hamzahaddaoui/AC-Adapter-with-Voltmeter/src/pic18f2420.h

#ifndef _PIC18F2420_H_
#define _PIC18F2420_H_

/*
 * C Header file for the Microchip PIC Microcontroller
 * PIC18F2420
 */
#ifndef _HTC_H_
#warning Header file pic18f2420.h included directly. Use #include <htc.h> instead.
#endif

/*
 * Register Definitions
 */

// Register: PORTA
extern volatile unsigned char           PORTA               @ 0xF80;
#ifndef _LIB_BUILD
asm("PORTA equ 0F80h");
#endif
// bitfield definitions
extern volatile union {
    struct {
        unsigned RA0                    :1;
        unsigned RA1                    :1;
        unsigned RA2                    :1;
        unsigned RA3                    :1;
        unsigned RA4                    :1;
        unsigned RA5                    :1;
        unsigned RA6                    :1;
        unsigned RA7                    :1;
    };
    struct {
        unsigned RA                     :8;
    };
    struct {
        unsigned AN0                    :1;
        unsigned AN1                    :1;
        unsigned AN2                    :1;
        unsigned AN3                    :1;
        unsigned T0CKI                  :1;
        unsigned AN4                    :1;
        unsigned OSC2                   :1;
        unsigned OSC1                   :1;
    };
    struct {
        unsigned                        :2;
        unsigned VREFN                  :1;
        unsigned VREFP                  :1;
        unsigned                        :1;
        unsigned SS                     :1;
        unsigned CLKO                   :1;
        unsigned CLKI                   :1;
    };
    struct {
        unsigned                        :5;
        unsigned NOT_SS                 :1;
    };
    struct {
        unsigned                        :2;
        unsigned CVREF                  :1;
        unsigned                        :2;
        unsigned nSS                    :1;
    };
    struct {
        unsigned                        :5;
        unsigned LVDIN                  :1;
    };
    struct {
        unsigned                        :5;
        unsigned HLVDIN                 :1;
    };
    struct {
        unsigned                        :4;
        unsigned C1OUT                  :1;
        unsigned C2OUT                  :1;
    };
    struct {
        unsigned                        :7;
        unsigned RJPU                   :1;
    };
    struct {
        unsigned ULPWUIN                :1;
    };
} PORTAbits @ 0xF80;

// Register: PORTB
extern volatile unsigned char           PORTB               @ 0xF81;
#ifndef _LIB_BUILD
asm("PORTB equ 0F81h");
#endif
// bitfield definitions
extern volatile union {
    struct {
        unsigned RB0                    :1;
        unsigned RB1                    :1;
        unsigned RB2                    :1;
        unsigned RB3                    :1;
        unsigned RB4                    :1;
        unsigned RB5                    :1;
        unsigned RB6                    :1;
        unsigned RB7                    :1;
    };
    struct {
        unsigned RB                     :8;
    };
    struct {
        unsigned INT0                   :1;
        unsigned INT1                   :1;
        unsigned INT2                   :1;
        unsigned CCP2                   :1;
        unsigned KBI0                   :1;
        unsigned KBI1                   :1;
        unsigned KBI2                   :1;
        unsigned KBI3                   :1;
    };
    struct {
        unsigned AN12                   :1;
        unsigned AN10                   :1;
        unsigned AN8                    :1;
        unsigned AN9                    :1;
        unsigned AN11                   :1;
        unsigned PGM                    :1;
        unsigned PGC                    :1;
        unsigned PGD                    :1;
    };
    struct {
        unsigned FLT0                   :1;
    };
    struct {
        unsigned                        :3;
        unsigned CCP2_PA2               :1;
    };
} PORTBbits @ 0xF81;

// Register: PORTC
extern volatile unsigned char           PORTC               @ 0xF82;
#ifndef _LIB_BUILD
asm("PORTC equ 0F82h");
#endif
// bitfield definitions
extern volatile union {
    struct {
        unsigned RC0                    :1;
        unsigned RC1                    :1;
        unsigned RC2                    :1;
        unsigned RC3                    :1;
        unsigned RC4                    :1;
        unsigned RC5                    :1;
        unsigned RC6                    :1;
        unsigned RC7                    :1;
    };
    struct {
        unsigned RC                     :8;
    };
    struct {
        unsigned T1OSO                  :1;
        unsigned T1OSI                  :1;
        unsigned CCP1                   :1;
        unsigned SCK                    :1;
        unsigned SDI                    :1;
        unsigned SDO                    :1;
        unsigned TX                     :1;
        unsigned RX                     :1;
    };
    struct {
        unsigned T13CKI                 :1;
        unsigned CCP2                   :1;
        unsigned                        :1;
        unsigned SCL                    :1;
        unsigned SDA                    :1;
        unsigned                        :1;
        unsigned CK                     :1;
        unsigned DT                     :1;
    };
    struct {
        unsigned T1CKI                  :1;
    };
    struct {
        unsigned                        :2;
        unsigned PA1                    :1;
    };
    struct {
        unsigned                        :1;
        unsigned PA2                    :1;
    };
} PORTCbits @ 0xF82;

// Register: PORTE
extern volatile unsigned char           PORTE               @ 0xF84;
#ifndef _LIB_BUILD
asm("PORTE equ 0F84h");
#endif
// bitfield definitions
extern volatile union {
    struct {
        unsigned                        :3;
        unsigned RE3                    :1;
    };
    struct {
        unsigned RE                     :8;
    };
    struct {
        unsigned                        :3;
        unsigned MCLR                   :1;
    };
    struct {
        unsigned                        :3;
        unsigned NOT_MCLR               :1;
    };
    struct {
        unsigned                        :3;
        unsigned nMCLR                  :1;
    };
    struct {
        unsigned                        :3;
        unsigned VPP                    :1;
    };
    struct {
        unsigned                        :2;
        unsigned CCP10                  :1;
    };
    struct {
        unsigned                        :7;
        unsigned CCP2E                  :1;
    };
    struct {
        unsigned                        :6;
        unsigned CCP6E                  :1;
    };
    struct {
        unsigned                        :5;
        unsigned CCP7E                  :1;
    };
    struct {
        unsigned                        :4;
        unsigned CCP8E                  :1;
    };
    struct {
        unsigned                        :3;
        unsigned CCP9E                  :1;
    };
    struct {
        unsigned                        :2;
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
        unsigned RB2                    :1;
        unsigned RB3                    :1;
        unsigned RB4                    :1;
        unsigned RB5                    :1;
        unsigned RB6                    :1;
        unsigned RB7                    :1;
    };
} DDRBbits @ 0xF93;

// Register: TRISC
extern volatile unsigned char           TRISC               @ 0xF94;
#ifndef _LIB_BUILD
asm("TRISC equ 0F94h");
#endif
// aliases
extern volatile unsigned char           DDRC                @ 0xF94;
#ifndef _LIB_BUILD
asm("DDRC equ 0F94h");
#endif
// bitfield definitions
extern volatile union {
    struct {
        unsigned TRISC0                 :1;
        unsigned TRISC1                 :1;
        unsigned TRISC2                 :1;
        unsigned TRISC3                 :1;
        unsigned TRISC4                 :1;
        unsigned TRISC5                 :1;
        unsigned TRISC6                 :1;
        unsigned TRISC7                 :1;
    };
    struct {
        unsigned TRISC                  :8;
    };
    struct {
        unsigned RC0                    :1;
        unsigned RC1                    :1;
        unsigned RC2                    :1;
        unsigned RC3                    :1;
        unsigned RC4                    :1;
        unsigned RC5                    :1;
        unsigned RC6                    :1;
        unsigned RC7                    :1;
    };
} TRISCbits @ 0xF94;
// alias bitfield definitions
extern volatile union {
    struct {
        unsigned TRISC0                 :1;
        unsigned TRISC1                 :1;
        unsigned TRISC2                 :1;
        unsigned TRISC3                 :1;
        unsigned TRISC4                 :1;
        unsigned TRISC5                 :1;
        unsigned TRISC6                 :1;
        unsigned TRISC7                 :1;
    };
    struct {
        unsigned TRISC                  :8;
    };
    struct {
        unsigned RC0                    :1;
        unsigned RC1                    :1;
        unsigned RC2                    :1;
        unsigned RC3                    :1;
        unsigned RC4                    :1;
        unsigned RC5                    :1;
        unsigned RC6                    :1;
        unsigned RC7                    :1;
    };
} DDRCbits @ 0xF94;

// Register: OSCTUNE
extern volatile unsigned char           OSCTUNE             @ 0xF9B;
#ifndef _LIB_BUILD
asm("OSCTUNE equ 0F9Bh");
#endif
// bitfield definitions
extern volatile union {
    struct {
        unsigned TUN                    :5;
        unsigned                        :1;
        unsigned PLLEN                  :1;
        unsigned INTSRC                 :1;
    };
    struct {
        unsigned TUN0                   :1;
        unsigned TUN1                   :1;
        unsigned TUN2                   :1;
        unsigned TUN3                   :1;
        unsigned TUN4                   :1;
    };
} OSCTUNEbits @ 0xF9B;

// Register: PIE1
extern volatile unsigned char           PIE1                @ 0xF9D;
#ifndef _LIB_BUILD
asm("PIE1 equ 0F9Dh");
#endif
// bitfield definitions
extern volatile union {
    struct {
        unsigned TMR1IE                 :1;
        unsigned TMR2IE                 :1;
        unsigned CCP1IE                 :1;
        unsigned SSPIE                  :1;
        unsigned TXIE                   :1;
        unsigned RCIE                   :1;
        unsigned ADIE                   :1;
    };
    struct {
        unsigned                        :5;
        unsigned RC1IE                  :1;
    };
    struct {
        unsigned                        :4;
        unsigned TX1IE                  :1;
    };
} PIE1bits @ 0xF9D;

// Register: PIR1
extern volatile unsigned char           PIR1                @ 0xF9E;
#ifndef _LIB_BUILD
asm("PIR1 equ 0F9Eh");
#endif
// bitfield definitions
extern volatile union {
    struct {
        unsigned TMR1IF                 :1;
        unsigned TMR2IF                 :1;
        unsigned CCP1IF                 :1;
        unsigned SSPIF                  :1;
        unsigned TXIF                   :1;
        unsigned RCIF                   :1;
        unsigned ADIF                   :1;
    };
    struct {
        unsigned TMR1IF                 :1;
        unsigned TMR2IF                 :1;
        unsigned CCP1IF                 :1;
        unsigned SSPIF                  :1;
        unsigned                        :2;
        unsigned ADIF                   :1;
    };
    struct {
        unsigned                        :5;
        unsigned RC1IF                  :1;
    };
    struct {
        unsigned                        :4;
        unsigned TX1IF                  :1;
    };
} PIR1bits @ 0xF9E;

// Register: IPR1
extern volatile unsigned char           IPR1                @ 0xF9F;
#ifndef _LIB_BUILD
asm("IPR1 equ 0F9Fh");
#endif
// bitfield definitions
extern volatile union {
    struct {
        unsigned TMR1IP                 :1;
        unsigned TMR2IP                 :1;
        unsigned CCP1IP                 :1;
        unsigned SSPIP                  :1;
        unsigned TXIP                   :1;
        unsigned RCIP                   :1;
        unsigned ADIP                   :1;
    };
    struct {
        unsigned                        :5;
        unsigned RC1IP                  :1;
    };
    struct {
        unsigned                        :4;
        unsigned TX1IP                  :1;
    };
} IPR1bits @ 0xF9F;

// Register: PIE2
extern volatile unsigned char           PIE2                @ 0xFA0;
#ifndef _LIB_BUILD
asm("PIE2 equ 0FA0h");
#endif
// bitfield definitions
extern volatile union {
    struct {
        unsigned CCP2IE                 :1;
        unsigned TMR3IE                 :1;
        unsigned HLVDIE                 :1;
        unsigned BCLIE                  :1;
        unsigned EEIE                   :1;
        unsigned                        :1;
        unsigned CMIE                   :1;
        unsigned OSCFIE                 :1;
    };
    struct {
        unsigned                        :2;
        unsigned LVDIE                  :1;
    };
} PIE2bits @ 0xFA0;

// Register: PIR2
extern volatile unsigned char           PIR2                @ 0xFA1;
#ifndef _LIB_BUILD
asm("PIR2 equ 0FA1h");
#endif
// bitfield definitions
extern volatile union {
    struct {
        unsigned CCP2IF                 :1;
        unsigned TMR3IF                 :1;
        unsigned HLVDIF                 :1;
        unsigned BCLIF                  :1;
        unsigned EEIF                   :1;
        unsigned                        :1;
        unsigned CMIF                   :1;
        unsigned OSCFIF                 :1;
    };
    struct {
        unsigned                        :2;
        unsigned LVDIF                  :1;
    };
} PIR2bits @ 0xFA1;

// Register: IPR2
extern volatile unsigned char           IPR2                @ 0xFA2;
#ifndef _LIB_BUILD
asm("IPR2 equ 0FA2h");
#endif
// bitfield definitions
extern volatile union {
    struct {
        unsigned CCP2IP                 :1;
        unsigned TMR3IP                 :1;
        unsigned HLVDIP                 :1;
        unsigned BCLIP                  :1;
        unsigned EEIP                   :1;
        unsigned                        :1;
        unsigned CMIP                   :1;
        unsigned OSCFIP                 :1;
    };
    struct {
        unsigned                        :2;
        unsigned LVDIP                  :1;
    };
} IPR2bits @ 0xFA2;

// Register: EECON1
extern volatile unsigned char           EECON1              @ 0xFA6;
#ifndef _LIB_BUILD
asm("EECON1 equ 0FA6h");
#endif
// bitfield definitions
extern volatile union {
    struct {
        unsigned RD                     :1;
        unsigned WR                     :1;
        unsigned WREN                   :1;
        unsigned WRERR                  :1;
        unsigned FREE                   :1;
        unsigned                        :1;
        unsigned CFGS                   :1;
        unsigned EEPGD                  :1;
    };
    struct {
        unsigned                        :6;
        unsigned EEFS                   :1;
    };
} EECON1bits @ 0xFA6;

// Register: EECON2
extern volatile unsigned char           EECON2              @ 0xFA7;
#ifndef _LIB_BUILD
asm("EECON2 equ 0FA7h");
#endif
// bitfield definitions
extern volatile union {
    struct {
        unsigned EECON2                 :8;
    };
} EECON2bits @ 0xFA7;

// Register: EEDATA
extern volatile unsigned char           EEDATA              @ 0xFA8;
#ifndef _LIB_BUILD
asm("EEDATA equ 0FA8h");
#endif
// bitfield definitions
extern volatile union {
    struct {
        unsigned EEDATA                 :8;
    };
} EEDATAbits @ 0xFA8;

// Register: EEADR
extern volatile unsigned char           EEADR               @ 0xFA9;
#ifndef _LIB_BUILD
asm("EEADR equ 0FA9h");
#endif
// bitfield definitions
extern volatile union {
    struct {
        unsigned EEADR                  :8;
    };
} EEADRbits @ 0xFA9;

// Register: RCSTA
extern volatile unsigned char           RCSTA               @ 0xFAB;
#ifndef _LIB_BUILD
asm("RCSTA equ 0FABh");
#endif
// aliases
extern volatile unsigned char           RCSTA1              @ 0xFAB;
#ifndef _LIB_BUILD
asm("RCSTA1 equ 0FABh");
#endif
// bitfield definitions
extern volatile union {
    struct {
        unsigned RX9D                   :1;
        unsigned OERR                   :1;
        unsigned FERR                   :1;
        unsigned ADDEN                  :1;
        unsigned CREN                   :1;
        unsigned SREN                   :1;
        unsigned RX9                    :1;
        unsigned SPEN                   :1;
    };
    struct {
        unsigned                        :3;
        unsigned ADEN                   :1;
    };
    struct {
        unsigned                        :5;
        unsigned SRENA                  :1;
    };
} RCSTAbits @ 0xFAB;
// alias bitfield definitions
extern volatile union {
    struct {
        unsigned RX9D                   :1;
        unsigned OERR                   :1;
        unsigned FERR                   :1;
        unsigned ADDEN                  :1;
        unsigned CREN                   :1;
        unsigned SREN                   :1;
        unsigned RX9                    :1;
        unsigned SPEN                   :1;
    };
    struct {
        unsigned                        :3;
        unsigned ADEN                   :1;
    };
    struct {
        unsigned                        :5;
        unsigned SRENA                  :1;
    };
} RCSTA1bits @ 0xFAB;

// Register: TXSTA
extern volatile unsigned char           TXSTA               @ 0xFAC;
#ifndef _LIB_BUILD
asm("TXSTA equ 0FACh");
#endif
// aliases
extern volatile unsigned char           TXSTA1              @ 0xFAC;
#ifndef _LIB_BUILD
asm("TXSTA1 equ 0FACh");
#endif
// bitfield definitions
extern volatile union {
    struct {
        unsigned TX9D                   :1;
        unsigned TRMT                   :1;
        unsigned BRGH                   :1;
        unsigned SENDB                  :1;
        unsigned SYNC                   :1;
        unsigned TXEN                   :1;
        unsigned TX9                    :1;
        unsigned CSRC                   :1;
    };
    struct {
        unsigned                        :2;
        unsigned BRGH1                  :1;
    };
    struct {
        unsigned                        :7;
        unsigned CSRC1                  :1;
    };
    struct {
        unsigned                        :3;
        unsigned SENDB1                 :1;
    };
    struct {
        unsigned                        :4;
        unsigned SYNC1                  :1;
    };
    struct {
        unsigned                        :1;
        unsigned TRMT1                  :1;
    };
    struct {
        unsigned                        :6;
        unsigned TX91                   :1;
    };
    struct {
        unsigned TX9D1                  :1;
    };
    struct {
        unsigned                        :5;
        unsigned TXEN1                  :1;
    };
} TXSTAbits @ 0xFAC;
// alias bitfield definitions
extern volatile union {
    struct {
        unsigned TX9D                   :1;
        unsigned TRMT                   :1;
        unsigned BRGH                   :1;
        unsigned SENDB                  :1;
        unsigned SYNC                   :1;
        unsigned TXEN                   :1;
        unsigned TX9                    :1;
        unsigned CSRC                   :1;
    };
    struct {
        unsigned                        :2;
        unsigned BRGH1                  :1;
    };
    struct {
        unsigned                        :7;
        unsigned CSRC1                  :1;
    };
    struct {
        unsigned                        :3;
        unsigned SENDB1                 :1;
    };
    struct {
        unsigned                        :4;
        unsigned SYNC1                  :1;
    };
    struct {
        unsigned                        :1;
        unsigned TRMT1                  :1;
    };
    struct {
        unsigned                        :6;
        unsigned TX91                   :1;
    };
    struct {
        unsigned TX9D1                  :1;
    };
    struct {
        unsigned                        :5;
        unsigned TXEN1                  :1;
    };
} TXSTA1bits @ 0xFAC;

// Register: TXREG
extern volatile unsigned char           TXREG               @ 0xFAD;
#ifndef _LIB_BUILD
asm("TXREG equ 0FADh");
#endif
// aliases
extern volatile unsigned char           TXREG1              @ 0xFAD;
#ifndef _LIB_BUILD
asm("TXREG1 equ 0FADh");
#endif
// bitfield definitions
extern volatile union {
    struct {
        unsigned TXREG                  :8;
    };
} TXREGbits @ 0xFAD;
// alias bitfield definitions
extern volatile union {
    struct {
        unsigned TXREG                  :8;
    };
} TXREG1bits @ 0xFAD;

// Register: RCREG
extern volatile unsigned char           RCREG               @ 0xFAE;
#ifndef _LIB_BUILD
asm("RCREG equ 0FAEh");
#endif
// aliases
extern volatile unsigned char           RCREG1              @ 0xFAE;
#ifndef _LIB_BUILD
asm("RCREG1 equ 0FAEh");
#endif
// bitfield definitions
extern volatile union {
    struct {
        unsigned RCREG                  :8;
    };
} RCREGbits @ 0xFAE;
// alias bitfield definitions
extern volatile union {
    struct {
        unsigned RCREG                  :8;
    };
} RCREG1bits @ 0xFAE;

// Register: SPBRG
extern volatile unsigned char           SPBRG               @ 0xFAF;
#ifndef _LIB_BUILD
asm("SPBRG equ 0FAFh");
#endif
// aliases
extern volatile unsigned char           SPBRG1              @ 0xFAF;
#ifndef _LIB_BUILD
asm("SPBRG1 equ 0FAFh");
#endif
// bitfield definitions
extern volatile union {
    struct {
        unsigned SPBRG                  :8;
    };
} SPBRGbits @ 0xFAF;
// alias bitfield definitions
extern volatile union {
    struct {
        unsigned SPBRG                  :8;
    };
} SPBRG1bits @ 0xFAF;

// Register: SPBRGH
extern volatile unsigned char           SPBRGH              @ 0xFB0;
#ifndef _LIB_BUILD
asm("SPBRGH equ 0FB0h");
#endif
// bitfield definitions
extern volatile union {
    struct {
        unsigned SPBRGH                 :8;
    };
} SPBRGHbits @ 0xFB0;

// Register: T3CON
extern volatile unsigned char           T3CON               @ 0xFB1;
#ifndef _LIB_BUILD
asm("T3CON equ 0FB1h");
#endif
// bitfield definitions
extern volatile union {
    struct {
        unsigned                        :2;
        unsigned NOT_T3SYNC             :1;
    };
    struct {
        unsigned TMR3ON                 :1;
        unsigned TMR3CS                 :1;
        unsigned nT3SYNC                :1;
        unsigned T3CCP1                 :1;
        unsigned T3CKPS                 :2;
        unsigned T3CCP2                 :1;
        unsigned RD16                   :1;
    };
    struct {
        unsigned                        :2;
        unsigned T3SYNC                 :1;
        unsigned                        :1;
        unsigned T3CKPS0                :1;
        unsigned T3CKPS1                :1;
    };
    struct {
        unsigned                        :7;
        unsigned RD163                  :1;
    };
    struct {
        unsigned                        :3;
        unsigned SOSCEN3                :1;
    };
    struct {
        unsigned                        :7;
        unsigned T3RD16                 :1;
    };
} T3CONbits @ 0xFB1;

// Register: TMR3
extern volatile unsigned short          TMR3                @ 0xFB2;
#ifndef _LIB_BUILD
asm("TMR3 equ 0FB2h");
#endif
// bitfield definitions
extern volatile union {
    struct {
        unsigned TMR3                   :16;
    };
} TMR3bits @ 0xFB2;

// Register: TMR3L
extern volatile unsigned char           TMR3L               @ 0xFB2;
#ifndef _LIB_BUILD
asm("TMR3L equ 0FB2h");
#endif
// bitfield definitions
extern volatile union {
    struct {
        unsigned TMR3L                  :8;
    };
} TMR3Lbits @ 0xFB2;

// Register: TMR3H
extern volatile unsigned char           TMR3H               @ 0xFB3;
#ifndef _LIB_BUILD
asm("TMR3H equ 0FB3h");
#endif
// bitfield definitions
extern volatile union {
    struct {
        unsigned TMR3H                  :8;
    };
} TMR3Hbits @ 0xFB3;

// Register: CMCON
extern volatile unsigned char           CMCON               @ 0xFB4;
#ifndef _LIB_BUILD
asm("CMCON equ 0FB4h");
#endif
// bitfield definitions
extern volatile union {
    struct {
        unsigned CM                     :3;
        unsigned CIS                    :1;
        unsigned C1INV                  :1;
        unsigned C2INV                  :1;
        unsigned C1OUT                  :1;
        unsigned C2OUT                  :1;
    };
    struct {
        unsigned CM0                    :1;
        unsigned CM1                    :1;
        unsigned CM2                    :1;
    };
    struct {
        unsigned CMEN0                  :1;
    };
    struct {
        unsigned                        :1;
        unsigned CMEN1                  :1;
    };
    struct {
        unsigned                        :2;
        unsigned CMEN2                  :1;
    };
} CMCONbits @ 0xFB4;

// Register: CVRCON
extern volatile unsigned char           CVRCON              @ 0xFB5;
#ifndef _LIB_BUILD
asm("CVRCON equ 0FB5h");
#endif
// bitfield definitions
extern volatile union {
    struct {
        unsigned CVR                    :4;
        unsigned CVRSS                  :1;
        unsigned CVRR                   :1;
        unsigned CVROE                  :1;
        unsigned CVREN                  :1;
    };
    struct {
        unsigned CVR0                   :1;
        unsigned CVR1                   :1;
        unsigned CVR2                   :1;
        unsigned CVR3                   :1;
    };
    struct {
        unsigned                        :6;
        unsigned CVROEN                 :1;
    };
} CVRCONbits @ 0xFB5;

// Register: ECCP1AS
extern volatile unsigned char           ECCP1AS             @ 0xFB6;
#ifndef _LIB_BUILD
asm("ECCP1AS equ 0FB6h");
#endif
// aliases
extern volatile unsigned char           ECCPAS              @ 0xFB6;
#ifndef _LIB_BUILD
asm("ECCPAS equ 0FB6h");
#endif
// bitfield definitions
extern volatile union {
    struct {
        unsigned                        :2;
        unsigned PSSAC                  :2;
        unsigned ECCPAS                 :3;
        unsigned ECCPASE                :1;
    };
    struct {
        unsigned                        :2;
        unsigned PSSAC0                 :1;
        unsigned PSSAC1                 :1;
        unsigned ECCPAS0                :1;
        unsigned ECCPAS1                :1;
        unsigned ECCPAS2                :1;
    };
} ECCP1ASbits @ 0xFB6;
// alias bitfield definitions
extern volatile union {
    struct {
        unsigned                        :2;
        unsigned PSSAC                  :2;
        unsigned ECCPAS                 :3;
        unsigned ECCPASE                :1;
    };
    struct {
        unsigned                        :2;
        unsigned PSSAC0                 :1;
        unsigned PSSAC1                 :1;
        unsigned ECCPAS0                :1;
        unsigned ECCPAS1                :1;
        unsigned ECCPAS2                :1;
    };
} ECCPASbits @ 0xFB6;

// Register: PWM1CON
extern volatile unsigned char           PWM1CON             @ 0xFB7;
#ifndef _LIB_BUILD
asm("PWM1CON equ 0FB7h");
#endif
// aliases
extern volatile unsigned char           ECCP1DEL            @ 0xFB7;
#ifndef _LIB_BUILD
asm("ECCP1DEL equ 0FB7h");
#endif
// bitfield definitions
extern volatile union {
    struct {
        unsigned                        :7;
        unsigned PRSEN                  :1;
    };
} PWM1CONbits @ 0xFB7;
// alias bitfield definitions
extern volatile union {
    struct {
        unsigned                        :7;
        unsigned PRSEN                  :1;
    };
} ECCP1DELbits @ 0xFB7;

// Register: BAUDCON
extern volatile unsigned char           BAUDCON             @ 0xFB8;
#ifndef _LIB_BUILD
asm("BAUDCON equ 0FB8h");
#endif
// aliases
extern volatile unsigned char           BAUDCTL             @ 0xFB8;
#ifndef _LIB_BUILD
asm("BAUDCTL equ 0FB8h");
#endif
// bitfield definitions
extern volatile union {
    struct {
        unsigned ABDEN                  :1;
        unsigned WUE                    :1;
        unsigned                        :1;
        unsigned BRG16                  :1;
        unsigned TXCKP                  :1;
        unsigned RXDTP                  :1;
        unsigned RCIDL                  :1;
        unsigned ABDOVF                 :1;
    };
    struct {
        unsigned                        :4;
        unsigned SCKP                   :1;
        unsigned                        :1;
        unsigned RCMT                   :1;
    };
    struct {
        unsigned                        :5;
        unsigned RXCKP                  :1;
    };
    struct {
        unsigned                        :1;
        unsigned W4E                    :1;
    };
} BAUDCONbits @ 0xFB8;
// alias bitfield definitions
extern volatile union {
    struct {
        unsigned ABDEN                  :1;
        unsigned WUE                    :1;
        unsigned                        :1;
        unsigned BRG16                  :1;
        unsigned TXCKP                  :1;
        unsigned RXDTP                  :1;
        unsigned RCIDL                  :1;
        unsigned ABDOVF                 :1;
    };
    struct {
        unsigned                        :4;
        unsigned SCKP                   :1;
        unsigned                        :1;
        unsigned RCMT                   :1;
    };
    struct {
        unsigned                        :5;
        unsigned RXCKP                  :1;
    };
    struct {
        unsigned                        :1;
        unsigned W4E                    :1;
    };
} BAUDCTLbits @ 0xFB8;

// Register: CCP2CON
extern volatile unsigned char           CCP2CON             @ 0xFBA;
#ifndef _LIB_BUILD
asm("CCP2CON equ 0FBAh");
#endif
// bitfield definitions
extern volatile union {
    struct {
        unsigned CCP2M                  :4;
        unsigned DC2B                   :2;
    };
    struct {
        unsigned CCP2M0                 :1;
        unsigned CCP2M1                 :1;
        unsigned CCP2M2                 :1;
        unsigned CCP2M3                 :1;
        unsigned CCP2Y                  :1;
        unsigned CCP2X                  :1;
    };
    struct {
        unsigned                        :4;
        unsigned DC2B0                  :1;
        unsigned DC2B1                  :1;
    };
} CCP2CONbits @ 0xFBA;

// Register: CCPR2
extern volatile unsigned short          CCPR2               @ 0xFBB;
#ifndef _LIB_BUILD
asm("CCPR2 equ 0FBBh");
#endif
// bitfield definitions
extern volatile union {
    struct {
        unsigned CCPR2                  :16;
    };
} CCPR2bits @ 0xFBB;

// Register: CCPR2L
extern volatile unsigned char           CCPR2L              @ 0xFBB;
#ifndef _LIB_BUILD
asm("CCPR2L equ 0FBBh");
#endif
// bitfield definitions
extern volatile union {
    struct {
        unsigned CCPR2L                 :8;
    };
} CCPR2Lbits @ 0xFBB;

// Register: CCPR2H
extern volatile unsigned char           CCPR2H              @ 0xFBC;
#ifndef _LIB_BUILD
asm("CCPR2H equ 0FBCh");
#endif
// bitfield definitions
extern volatile union {
    struct {
        unsigned CCPR2H                 :8;
    };
} CCPR2Hbits @ 0xFBC;

// Register: CCP1CON
extern volatile unsigned char           CCP1CON             @ 0xFBD;
#ifndef _LIB_BUILD
asm("CCP1CON equ 0FBDh");
#endif
// bitfield definitions
extern volatile union {
    struct {
        unsigned CCP1M                  :4;
        unsigned DC1B                   :2;
    };
    struct {
        unsigned CCP1M0                 :1;
        unsigned CCP1M1                 :1;
        unsigned CCP1M2                 :1;
        unsigned CCP1M3                 :1;
        unsigned CCP1Y                  :1;
        unsigned CCP1X                  :1;
    };
    struct {
        unsigned                        :4;
        unsigned DC1B0                  :1;
        unsigned DC1B1                  :1;
    };
} CCP1CONbits @ 0xFBD;

// Register: CCPR1
extern volatile unsigned short          CCPR1               @ 0xFBE;
#ifndef _LIB_BUILD
asm("CCPR1 equ 0FBEh");
#endif
// bitfield definitions
extern volatile union {
    struct {
        unsigned CCPR1                  :16;
    };
} CCPR1bits @ 0xFBE;

// Register: CCPR1L
extern volatile unsigned char           CCPR1L              @ 0xFBE;
#ifndef _LIB_BUILD
asm("CCPR1L equ 0FBEh");
#endif
// bitfield definitions
extern volatile union {
    struct {
        unsigned CCPR1L                 :8;
    };
} CCPR1Lbits @ 0xFBE;

// Register: CCPR1H
extern volatile unsigned char           CCPR1H              @ 0xFBF;
#ifndef _LIB_BUILD
asm("CCPR1H equ 0FBFh");
#endif
// bitfield definitions
extern volatile union {
    struct {
        unsigned CCPR1H                 :8;
    };
} CCPR1Hbits @ 0xFBF;

// Register: ADCON2
extern volatile unsigned char           ADCON2              @ 0xFC0;
#ifndef _LIB_BUILD
asm("ADCON2 equ 0FC0h");
#endif
// bitfield definitions
extern volatile union {
    struct {
        unsigned ADCS                   :3;
        unsigned ACQT                   :3;
        unsigned                        :1;
        unsigned ADFM                   :1;
    };
    struct {
        unsigned ADCS0                  :1;
        unsigned ADCS1                  :1;
        unsigned ADCS2                  :1;
        unsigned ACQT0                  :1;
        unsigned ACQT1                  :1;
        unsigned ACQT2                  :1;
    };
} ADCON2bits @ 0xFC0;

// Register: ADCON1
extern volatile unsigned char           ADCON1              @ 0xFC1;
#ifndef _LIB_BUILD
asm("ADCON1 equ 0FC1h");
#endif
// bitfield definitions
extern volatile union {
    struct {
        unsigned PCFG                   :4;
        unsigned VCFG                   :2;
    };
    struct {
        unsigned PCFG0                  :1;
        unsigned PCFG1                  :1;
        unsigned PCFG2                  :1;
        unsigned PCFG3                  :1;
        unsigned VCFG0                  :1;
        unsigned VCFG1                  :1;
    };
    struct {
        unsigned                        :3;
        unsigned CHSN3                  :1;
    };
    struct {
        unsigned                        :4;
        unsigned VCFG01                 :1;
    };
    struct {
        unsigned                        :5;
        unsigned VCFG11                 :1;
    };
} ADCON1bits @ 0xFC1;

// Register: ADCON0
extern volatile unsigned char           ADCON0              @ 0xFC2;
#ifndef _LIB_BUILD
asm("ADCON0 equ 0FC2h");
#endif
// bitfield definitions
extern volatile union {
    struct {
        unsigned                        :1;
        unsigned GO_NOT_DONE            :1;
    };
    struct {
        unsigned ADON                   :1;
        unsigned GO_nDONE               :1;
        unsigned CHS                    :4;
    };
    struct {
        unsigned                        :1;
        unsigned GO_NOT_DONE            :1;
    };
    struct {
        unsigned ADON                   :1;
        unsigned GO_nDONE               :1;
        unsigned CHS                    :4;
    };
    struct {
        unsigned                        :1;
        unsigned GO                     :1;
        unsigned CHS0                   :1;
        unsigned CHS1                   :1;
        unsigned CHS2                   :1;
        unsigned CHS3                   :1;
    };
    struct {
        unsigned                        :1;
        unsigned DONE                   :1;
    };
    struct {
        unsigned                        :1;
        unsigned NOT_DONE               :1;
    };
    struct {
        unsigned                        :1;
        unsigned nDONE                  :1;
    };
    struct {
        unsigned                        :1;
        unsigned GO_DONE                :1;
    };
    struct {
        unsigned                        :1;
        unsigned GODONE                 :1;
    };
} ADCON0bits @ 0xFC2;

// Register: ADRES
extern volatile unsigned short          ADRES               @ 0xFC3;
#ifndef _LIB_BUILD
asm("ADRES equ 0FC3h");
#endif
// bitfield definitions
extern volatile union {
    struct {
        unsigned ADRES                  :16;
    };
} ADRESbits @ 0xFC3;

// Register: ADRESL
extern volatile unsigned char           ADRESL              @ 0xFC3;
#ifndef _LIB_BUILD
asm("ADRESL equ 0FC3h");
#endif
// bitfield definitions
extern volatile union {
    struct {
        unsigned ADRESL                 :8;
    };
} ADRESLbits @ 0xFC3;

// Register: ADRESH
extern volatile unsigned char           ADRESH              @ 0xFC4;
#ifndef _LIB_BUILD
asm("ADRESH equ 0FC4h");
#endif
// bitfield definitions
extern volatile union {
    struct {
        unsigned ADRESH                 :8;
    };
} ADRESHbits @ 0xFC4;

// Register: SSPCON2
extern volatile unsigned char           SSPCON2             @ 0xFC5;
#ifndef _LIB_BUILD
asm("SSPCON2 equ 0FC5h");
#endif
// bitfield definitions
extern volatile union {
    struct {
        unsigned SEN                    :1;
        unsigned RSEN                   :1;
        unsigned PEN                    :1;
        unsigned RCEN                   :1;
        unsigned ACKEN                  :1;
        unsigned ACKDT                  :1;
        unsigned ACKSTAT                :1;
        unsigned GCEN                   :1;
    };
    struct {
        unsigned                        :1;
        unsigned ADMSK1                 :1;
        unsigned ADMSK2                 :1;
        unsigned ADMSK3                 :1;
        unsigned ADMSK4                 :1;
        unsigned ADMSK5                 :1;
    };
} SSPCON2bits @ 0xFC5;

// Register: SSPCON1
extern volatile unsigned char           SSPCON1             @ 0xFC6;
#ifndef _LIB_BUILD
asm("SSPCON1 equ 0FC6h");
#endif
// bitfield definitions
extern volatile union {
    struct {
        unsigned SSPM                   :4;
        unsigned CKP                    :1;
        unsigned SSPEN                  :1;
        unsigned SSPOV                  :1;
        unsigned WCOL                   :1;
    };
    struct {
        unsigned SSPM0                  :1;
        unsigned SSPM1                  :1;
        unsigned SSPM2                  :1;
        unsigned SSPM3                  :1;
    };
} SSPCON1bits @ 0xFC6;

// Register: SSPSTAT
extern volatile unsigned char           SSPSTAT             @ 0xFC7;
#ifndef _LIB_BUILD
asm("SSPSTAT equ 0FC7h");
#endif
// bitfield definitions
extern volatile union {
    struct {
        unsigned                        :2;
        unsigned R_NOT_W                :1;
    };
    struct {
        unsigned                        :5;
        unsigned D_NOT_A                :1;
    };
    struct {
        unsigned BF                     :1;
        unsigned UA                     :1;
        unsigned R_nW                   :1;
        unsigned S                      :1;
        unsigned P                      :1;
        unsigned D_nA                   :1;
        unsigned CKE                    :1;
        unsigned SMP                    :1;
    };
    struct {
        unsigned                        :2;
        unsigned R_NOT_W                :1;
    };
    struct {
        unsigned                        :5;
        unsigned D_NOT_A                :1;
    };
    struct {
        unsigned BF                     :1;
        unsigned UA                     :1;
        unsigned R_nW                   :1;
        unsigned S                      :1;
        unsigned P                      :1;
        unsigned D_nA                   :1;
        unsigned CKE                    :1;
        unsigned SMP                    :1;
    };
    struct {
        unsigned                        :2;
        unsigned R                      :1;
        unsigned                        :2;
        unsigned D                      :1;
    };
    struct {
        unsigned                        :2;
        unsigned W                      :1;
        unsigned                        :2;
        unsigned A                      :1;
    };
    struct {
        unsigned                        :2;
        unsigned nW                     :1;
        unsigned                        :2;
        unsigned nA                     :1;
    };
    struct {
        unsigned                        :2;
        unsigned R_W                    :1;
        unsigned                        :2;
        unsigned D_A                    :1;
    };
    struct {
        unsigned                        :2;
        unsigned NOT_WRITE              :1;
    };
    struct {
        unsigned                        :5;
        unsigned NOT_ADDRESS            :1;
    };
    struct {
        unsigned                        :2;
        unsigned nWRITE                 :1;
        unsigned                        :2;
        unsigned nADDRESS               :1;
    };
    struct {
        unsigned                        :5;
        unsigned DA                     :1;
    };
    struct {
        unsigned                        :2;
        unsigned RW                     :1;
    };
    struct {
        unsigned                        :3;
        unsigned START                  :1;
    };
    struct {
        unsigned                        :4;
        unsigned STOP                   :1;
    };
    struct {
        unsigned                        :2;
        unsigned NOT_W                  :1;
    };
    struct {
        unsigned                        :5;
        unsigned NOT_A                  :1;
    };
} SSPSTATbits @ 0xFC7;

// Register: SSPADD
extern volatile unsigned char           SSPADD              @ 0xFC8;
#ifndef _LIB_BUILD
asm("SSPADD equ 0FC8h");
#endif
// bitfield definitions
extern volatile union {
    struct {
        unsigned SSPADD                 :8;
    };
} SSPADDbits @ 0xFC8;

// Register: SSPBUF
extern volatile unsigned char           SSPBUF              @ 0xFC9;
#ifndef _LIB_BUILD
asm("SSPBUF equ 0FC9h");
#endif
// bitfield definitions
extern volatile union {
    struct {
        unsigned SSPBUF                 :8;
    };
} SSPBUFbits @ 0xFC9;

// Register: T2CON
extern volatile unsigned char           T2CON               @ 0xFCA;
#ifndef _LIB_BUILD
asm("T2CON equ 0FCAh");
#endif
// bitfield definitions
extern volatile union {
    struct {
        unsigned T2CKPS                 :2;
        unsigned TMR2ON                 :1;
        unsigned T2OUTPS                :4;
    };
    struct {
        unsigned T2CKPS0                :1;
        unsigned T2CKPS1                :1;
        unsigned                        :1;
        unsigned T2OUTPS0               :1;
        unsigned T2OUTPS1               :1;
        unsigned T2OUTPS2               :1;
        unsigned T2OUTPS3               :1;
    };
    struct {
        unsigned                        :3;
        unsigned TOUTPS0                :1;
        unsigned TOUTPS1                :1;
        unsigned TOUTPS2                :1;
        unsigned TOUTPS3                :1;
    };
} T2CONbits @ 0xFCA;

// Register: PR2
extern volatile unsigned char           PR2                 @ 0xFCB;
#ifndef _LIB_BUILD
asm("PR2 equ 0FCBh");
#endif
// aliases
extern volatile unsigned char           MEMCON              @ 0xFCB;
#ifndef _LIB_BUILD
asm("MEMCON equ 0FCBh");
#endif
// bitfield definitions
extern volatile union {
    struct {
        unsigned PR2                    :8;
    };
} PR2bits @ 0xFCB;
// alias bitfield definitions
extern volatile union {
    struct {
        unsigned PR2                    :8;
    };
} MEMCONbits @ 0xFCB;

// Register: TMR2
extern volatile unsigned char           TMR2                @ 0xFCC;
#ifndef _LIB_BUILD
asm("TMR2 equ 0FCCh");
#endif
// bitfield definitions
extern volatile union {
    struct {
        unsigned TMR2                   :8;
    };
} TMR2bits @ 0xFCC;

// Register: T1CON
extern volatile unsigned char           T1CON               @ 0xFCD;
#ifndef _LIB_BUILD
asm("T1CON equ 0FCDh");
#endif
// bitfield definitions
extern volatile union {
    struct {
        unsigned                        :2;
        unsigned NOT_T1SYNC             :1;
    };
    struct {
        unsigned TMR1ON                 :1;
        unsigned TMR1CS                 :1;
        unsigned nT1SYNC                :1;
        unsigned T1OSCEN                :1;
        unsigned T1CKPS                 :2;
        unsigned T1RUN                  :1;
        unsigned RD16                   :1;
    };
    struct {
        unsigned                        :2;
        unsigned T1SYNC                 :1;
        unsigned                        :1;
        unsigned T1CKPS0                :1;
        unsigned T1CKPS1                :1;
    };
    struct {
        unsigned                        :3;
        unsigned SOSCEN                 :1;
    };
    struct {
        unsigned                        :7;
        unsigned T1RD16                 :1;
    };
} T1CONbits @ 0xFCD;

// Register: TMR1
extern volatile unsigned short          TMR1                @ 0xFCE;
#ifndef _LIB_BUILD
asm("TMR1 equ 0FCEh");
#endif
// bitfield definitions
extern volatile union {
    struct {
        unsigned TMR1                   :16;
    };
} TMR1bits @ 0xFCE;

// Register: TMR1L
extern volatile unsigned char           TMR1L               @ 0xFCE;
#ifndef _LIB_BUILD
asm("TMR1L equ 0FCEh");
#endif
// bitfield definitions
extern volatile union {
    struct {
        unsigned TMR1L                  :8;
    };
} TMR1Lbits @ 0xFCE;

// Register: TMR1H
extern volatile unsigned char           TMR1H               @ 0xFCF;
#ifndef _LIB_BUILD
asm("TMR1H equ 0FCFh");
#endif
// bitfield definitions
extern volatile union {
    struct {
        unsigned TMR1H                  :8;
    };
} TMR1Hbits @ 0xFCF;

// Register: RCON
extern volatile unsigned char           RCON                @ 0xFD0;
#ifndef _LIB_BUILD
asm("RCON equ 0FD0h");
#endif
// bitfield definitions
extern volatile union {
    struct {
        unsigned NOT_BOR                :1;
    };
    struct {
        unsigned                        :1;
        unsigned NOT_POR                :1;
    };
    struct {
        unsigned                        :2;
        unsigned NOT_PD                 :1;
    };
    struct {
        unsigned                        :3;
        unsigned NOT_TO                 :1;
    };
    struct {
        unsigned                        :4;
        unsigned NOT_RI                 :1;
    };
    struct {
        unsigned nBOR                   :1;
        unsigned nPOR                   :1;
        unsigned nPD                    :1;
        unsigned nTO                    :1;
        unsigned nRI                    :1;
        unsigned                        :1;
        unsigned SBOREN                 :1;
        unsigned IPEN                   :1;
    };
    struct {
        unsigned BOR                    :1;
        unsigned POR                    :1;
        unsigned PD                     :1;
        unsigned TO                     :1;
        unsigned RI                     :1;
    };
} RCONbits @ 0xFD0;

// Register: WDTCON
extern volatile unsigned char           WDTCON              @ 0xFD1;
#ifndef _LIB_BUILD
asm("WDTCON equ 0FD1h");
#endif
// bitfield definitions
extern volatile union {
    struct {
        unsigned SWDTEN                 :1;
    };
    struct {
        unsigned SWDTE                  :1;
    };
} WDTCONbits @ 0xFD1;

// Register: HLVDCON
extern volatile unsigned char           HLVDCON             @ 0xFD2;
#ifndef _LIB_BUILD
asm("HLVDCON equ 0FD2h");
#endif
// aliases
extern volatile unsigned char           LVDCON              @ 0xFD2;
#ifndef _LIB_BUILD
asm("LVDCON equ 0FD2h");
#endif
// bitfield definitions
extern volatile union {
    struct {
        unsigned HLVDL                  :4;
        unsigned HLVDEN                 :1;
        unsigned IVRST                  :1;
        unsigned                        :1;
        unsigned VDIRMAG                :1;
    };
    struct {
        unsigned HLVDL0                 :1;
        unsigned HLVDL1                 :1;
        unsigned HLVDL2                 :1;
        unsigned HLVDL3                 :1;
    };
    struct {
        unsigned LVDL0                  :1;
        unsigned LVDL1                  :1;
        unsigned LVDL2                  :1;
        unsigned LVDL3                  :1;
        unsigned LVDEN                  :1;
        unsigned IRVST                  :1;
    };
    struct {
        unsigned LVV0                   :1;
        unsigned LVV1                   :1;
        unsigned LVV2                   :1;
        unsigned LVV3                   :1;
        unsigned                        :1;
        unsigned BGST                   :1;
    };
} HLVDCONbits @ 0xFD2;
// alias bitfield definitions
extern volatile union {
    struct {
        unsigned HLVDL                  :4;
        unsigned HLVDEN                 :1;
        unsigned IVRST                  :1;
        unsigned                        :1;
        unsigned VDIRMAG                :1;
    };
    struct {
        unsigned HLVDL0                 :1;
        unsigned HLVDL1                 :1;
        unsigned HLVDL2                 :1;
        unsigned HLVDL3                 :1;
    };
    struct {
        unsigned LVDL0                  :1;
        unsigned LVDL1                  :1;
        unsigned LVDL2                  :1;
        unsigned LVDL3                  :1;
        unsigned LVDEN                  :1;
        unsigned IRVST                  :1;
    };
    struct {
        unsigned LVV0                   :1;
        unsigned LVV1                   :1;
        unsigned LVV2                   :1;
        unsigned LVV3                   :1;
        unsigned                        :1;
        unsigned BGST                   :1;
    };
} LVDCONbits @ 0xFD2;

// Register: OSCCON
extern volatile unsigned char           OSCCON              @ 0xFD3;
#ifndef _LIB_BUILD
asm("OSCCON equ 0FD3h");
#endif
// bitfield definitions
extern volatile union {
    struct {
        unsigned SCS                    :2;
        unsigned IOFS                   :1;
        unsigned OSTS                   :1;
        unsigned IRCF                   :3;
        unsigned IDLEN                  :1;
    };
    struct {
        unsigned SCS0                   :1;
        unsigned SCS1                   :1;
        unsigned FLTS                   :1;
        unsigned                        :1;
        unsigned IRCF0                  :1;
        unsigned IRCF1                  :1;
        unsigned IRCF2                  :1;
    };
} OSCCONbits @ 0xFD3;

// Register: T0CON
extern volatile unsigned char           T0CON               @ 0xFD5;
#ifndef _LIB_BUILD
asm("T0CON equ 0FD5h");
#endif
// bitfield definitions
extern volatile union {
    struct {
        unsigned T0PS                   :3;
        unsigned PSA                    :1;
        unsigned T0SE                   :1;
        unsigned T0CS                   :1;
        unsigned T08BIT                 :1;
        unsigned TMR0ON                 :1;
    };
    struct {
        unsigned T0PS0                  :1;
        unsigned T0PS1                  :1;
        unsigned T0PS2                  :1;
        unsigned T0PS3                  :1;
        unsigned                        :2;
        unsigned T016BIT                :1;
    };
} T0CONbits @ 0xFD5;

// Register: TMR0
extern volatile unsigned short          TMR0                @ 0xFD6;
#ifndef _LIB_BUILD
asm("TMR0 equ 0FD6h");
#endif
// bitfield definitions
extern volatile union {
    struct {
        unsigned TMR0                   :16;
    };
} TMR0bits @ 0xFD6;

// Register: TMR0L
extern volatile unsigned char           TMR0L               @ 0xFD6;
#ifndef _LIB_BUILD
asm("TMR0L equ 0FD6h");
#endif
// bitfield definitions
extern volatile union {
    struct {
        unsigned TMR0L                  :8;
    };
} TMR0Lbits @ 0xFD6;

// Register: TMR0H
extern volatile unsigned char           TMR0H               @ 0xFD7;
#ifndef _LIB_BUILD
asm("TMR0H equ 0FD7h");
#endif
// bitfield definitions
extern volatile union {
    struct {
        unsigned TMR0H                  :8;
    };
} TMR0Hbits @ 0xFD7;

// Register: STATUS
extern volatile unsigned char           STATUS              @ 0xFD8;
#ifndef _LIB_BUILD
asm("STATUS equ 0FD8h");
#endif
// bitfield definitions
extern volatile union {
    struct {
        unsigned C                      :1;
        unsigned DC                     :1;
        unsigned Z                      :1;
        unsigned OV                     :1;
        unsigned N                      :1;
    };
    struct {
        unsigned CARRY                  :1;
    };
    struct {
        unsigned                        :4;
        unsigned NEGATIVE               :1;
    };
    struct {
        unsigned                        :3;
        unsigned OVERFLOW               :1;
    };
    struct {
        unsigned                        :2;
        unsigned ZERO                   :1;
    };
} STATUSbits @ 0xFD8;

// Register: FSR2
extern volatile unsigned short          FSR2                @ 0xFD9;
#ifndef _LIB_BUILD
asm("FSR2 equ 0FD9h");
#endif
// bitfield definitions
extern volatile union {
    struct {
        unsigned FSR2                   :12;
    };
} FSR2bits @ 0xFD9;

// Register: FSR2L
extern volatile unsigned char           FSR2L               @ 0xFD9;
#ifndef _LIB_BUILD
asm("FSR2L equ 0FD9h");
#endif
// bitfield definitions
extern volatile union {
    struct {
        unsigned FSR2L                  :8;
    };
} FSR2Lbits @ 0xFD9;

// Register: FSR2H
extern volatile unsigned char           FSR2H               @ 0xFDA;
#ifndef _LIB_BUILD
asm("FSR2H equ 0FDAh");
#endif
// bitfield definitions
extern volatile union {
    struct {
        unsigned FSR2H                  :4;
    };
} FSR2Hbits @ 0xFDA;

// Register: PLUSW2
extern volatile unsigned char           PLUSW2              @ 0xFDB;
#ifndef _LIB_BUILD
asm("PLUSW2 equ 0FDBh");
#endif
// bitfield definitions
extern volatile union {
    struct {
        unsigned PLUSW2                 :8;
    };
} PLUSW2bits @ 0xFDB;

// Register: PREINC2
extern volatile unsigned char           PREINC2             @ 0xFDC;
#ifndef _LIB_BUILD
asm("PREINC2 equ 0FDCh");
#endif
// bitfield definitions
extern volatile union {
    struct {
        unsigned PREINC2                :8;
    };
} PREINC2bits @ 0xFDC;

// Register: POSTDEC2
extern volatile unsigned char           POSTDEC2            @ 0xFDD;
#ifndef _LIB_BUILD
asm("POSTDEC2 equ 0FDDh");
#endif
// bitfield definitions
extern volatile union {
    struct {
        unsigned POSTDEC2               :8;
    };
} POSTDEC2bits @ 0xFDD;

// Register: POSTINC2
extern volatile unsigned char           POSTINC2            @ 0xFDE;
#ifndef _LIB_BUILD
asm("POSTINC2 equ 0FDEh");
#endif
// bitfield definitions
extern volatile union {
    struct {
        unsigned POSTINC2               :8;
    };
} POSTINC2bits @ 0xFDE;

// Register: INDF2
extern volatile unsigned char           INDF2               @ 0xFDF;
#ifndef _LIB_BUILD
asm("INDF2 equ 0FDFh");
#endif
// bitfield definitions
extern volatile union {
    struct {
        unsigned INDF2                  :8;
    };
} INDF2bits @ 0xFDF;

// Register: BSR
extern volatile unsigned char           BSR                 @ 0xFE0;
#ifndef _LIB_BUILD
asm("BSR equ 0FE0h");
#endif
// bitfield definitions
extern volatile union {
    struct {
        unsigned BSR                    :4;
    };
} BSRbits @ 0xFE0;

// Register: FSR1
extern volatile unsigned short          FSR1                @ 0xFE1;
#ifndef _LIB_BUILD
asm("FSR1 equ 0FE1h");
#endif
// bitfield definitions
extern volatile union {
    struct {
        unsigned FSR1                   :12;
    };
} FSR1bits @ 0xFE1;

// Register: FSR1L
extern volatile unsigned char           FSR1L               @ 0xFE1;
#ifndef _LIB_BUILD
asm("FSR1L equ 0FE1h");
#endif
// bitfield definitions
extern volatile union {
    struct {
        unsigned FSR1L                  :8;
    };
} FSR1Lbits @ 0xFE1;

// Register: FSR1H
extern volatile unsigned char           FSR1H               @ 0xFE2;
#ifndef _LIB_BUILD
asm("FSR1H equ 0FE2h");
#endif
// bitfield definitions
extern volatile union {
    struct {
        unsigned FSR1H                  :4;
    };
} FSR1Hbits @ 0xFE2;

// Register: PLUSW1
extern volatile unsigned char           PLUSW1              @ 0xFE3;
#ifndef _LIB_BUILD
asm("PLUSW1 equ 0FE3h");
#endif
// bitfield definitions
extern volatile union {
    struct {
        unsigned PLUSW1                 :8;
    };
} PLUSW1bits @ 0xFE3;

// Register: PREINC1
extern volatile unsigned char           PREINC1             @ 0xFE4;
#ifndef _LIB_BUILD
asm("PREINC1 equ 0FE4h");
#endif
// bitfield definitions
extern volatile union {
    struct {
        unsigned PREINC1                :8;
    };
} PREINC1bits @ 0xFE4;

// Register: POSTDEC1
extern volatile unsigned char           POSTDEC1            @ 0xFE5;
#ifndef _LIB_BUILD
asm("POSTDEC1 equ 0FE5h");
#endif
// bitfield definitions
extern volatile union {
    struct {
        unsigned POSTDEC1               :8;
    };
} POSTDEC1bits @ 0xFE5;

// Register: POSTINC1
extern volatile unsigned char           POSTINC1            @ 0xFE6;
#ifndef _LIB_BUILD
asm("POSTINC1 equ 0FE6h");
#endif
// bitfield definitions
extern volatile union {
    struct {
        unsigned POSTINC1               :8;
    };
} POSTINC1bits @ 0xFE6;

// Register: INDF1
extern volatile unsigned char           INDF1               @ 0xFE7;
#ifndef _LIB_BUILD
asm("INDF1 equ 0FE7h");
#endif
// bitfield definitions
extern volatile union {
    struct {
        unsigned INDF1                  :8;
    };
} INDF1bits @ 0xFE7;

// Register: WREG
extern volatile unsigned char           WREG                @ 0xFE8;
#ifndef _LIB_BUILD
asm("WREG equ 0FE8h");
#endif
// aliases
// extern volatile unsigned char           W                   @ 0xFE8;
#ifndef _LIB_BUILD
// asm("W equ 0FE8h");
#endif
// bitfield definitions
extern volatile union {
    struct {
        unsigned WREG                   :8;
    };
} WREGbits @ 0xFE8;
// alias bitfield definitions
extern volatile union {
    struct {
        unsigned WREG                   :8;
    };
} Wbits @ 0xFE8;

// Register: FSR0
extern volatile unsigned short          FSR0                @ 0xFE9;
#ifndef _LIB_BUILD
asm("FSR0 equ 0FE9h");
#endif
// bitfield definitions
extern volatile union {
    struct {
        unsigned FSR0                   :12;
    };
} FSR0bits @ 0xFE9;

// Register: FSR0L
extern volatile unsigned char           FSR0L               @ 0xFE9;
#ifndef _LIB_BUILD
asm("FSR0L equ 0FE9h");
#endif
// bitfield definitions
extern volatile union {
    struct {
        unsigned FSR0L                  :8;
    };
} FSR0Lbits @ 0xFE9;

// Register: FSR0H
extern volatile unsigned char           FSR0H               @ 0xFEA;
#ifndef _LIB_BUILD
asm("FSR0H equ 0FEAh");
#endif
// bitfield definitions
extern volatile union {
    struct {
        unsigned FSR0H                  :4;
    };
} FSR0Hbits @ 0xFEA;

// Register: PLUSW0
extern volatile unsigned char           PLUSW0              @ 0xFEB;
#ifndef _LIB_BUILD
asm("PLUSW0 equ 0FEBh");
#endif
// bitfield definitions
extern volatile union {
    struct {
        unsigned PLUSW0                 :8;
    };
} PLUSW0bits @ 0xFEB;

// Register: PREINC0
extern volatile unsigned char           PREINC0             @ 0xFEC;
#ifndef _LIB_BUILD
asm("PREINC0 equ 0FECh");
#endif
// bitfield definitions
extern volatile union {
    struct {
        unsigned PREINC0                :8;
    };
} PREINC0bits @ 0xFEC;

// Register: POSTDEC0
extern volatile unsigned char           POSTDEC0            @ 0xFED;
#ifndef _LIB_BUILD
asm("POSTDEC0 equ 0FEDh");
#endif
// bitfield definitions
extern volatile union {
    struct {
        unsigned POSTDEC0               :8;
    };
} POSTDEC0bits @ 0xFED;

// Register: POSTINC0
extern volatile unsigned char           POSTINC0            @ 0xFEE;
#ifndef _LIB_BUILD
asm("POSTINC0 equ 0FEEh");
#endif
// bitfield definitions
extern volatile union {
    struct {
        unsigned POSTINC0               :8;
    };
} POSTINC0bits @ 0xFEE;

// Register: INDF0
extern volatile unsigned char           INDF0               @ 0xFEF;
#ifndef _LIB_BUILD
asm("INDF0 equ 0FEFh");
#endif
// bitfield definitions
extern volatile union {
    struct {
        unsigned INDF0                  :8;
    };
} INDF0bits @ 0xFEF;

// Register: INTCON3
extern volatile unsigned char           INTCON3             @ 0xFF0;
#ifndef _LIB_BUILD
asm("INTCON3 equ 0FF0h");
#endif
// bitfield definitions
extern volatile union {
    struct {
        unsigned INT1IF                 :1;
        unsigned INT2IF                 :1;
        unsigned                        :1;
        unsigned INT1IE                 :1;
        unsigned INT2IE                 :1;
        unsigned                        :1;
        unsigned INT1IP                 :1;
        unsigned INT2IP                 :1;
    };
    struct {
        unsigned INT1F                  :1;
        unsigned INT2F                  :1;
        unsigned                        :1;
        unsigned INT1E                  :1;
        unsigned INT2E                  :1;
        unsigned                        :1;
        unsigned INT1P                  :1;
        unsigned INT2P                  :1;
    };
} INTCON3bits @ 0xFF0;

// Register: INTCON2
extern volatile unsigned char           INTCON2             @ 0xFF1;
#ifndef _LIB_BUILD
asm("INTCON2 equ 0FF1h");
#endif
// bitfield definitions
extern volatile union {
    struct {
        unsigned                        :7;
        unsigned NOT_RBPU               :1;
    };
    struct {
        unsigned RBIP                   :1;
        unsigned                        :1;
        unsigned TMR0IP                 :1;
        unsigned                        :1;
        unsigned INTEDG2                :1;
        unsigned INTEDG1                :1;
        unsigned INTEDG0                :1;
        unsigned nRBPU                  :1;
    };
    struct {
        unsigned                        :7;
        unsigned RBPU                   :1;
    };
} INTCON2bits @ 0xFF1;

// Register: INTCON
extern volatile unsigned char           INTCON              @ 0xFF2;
#ifndef _LIB_BUILD
asm("INTCON equ 0FF2h");
#endif
// bitfield definitions
extern volatile union {
    struct {
        unsigned RBIF                   :1;
        unsigned INT0IF                 :1;
        unsigned TMR0IF                 :1;
        unsigned RBIE                   :1;
        unsigned INT0IE                 :1;
        unsigned TMR0IE                 :1;
        unsigned PEIE_GIEL              :1;
        unsigned GIE_GIEH               :1;
    };
    struct {
        unsigned RBIF                   :1;
        unsigned INT0IF                 :1;
        unsigned TMR0IF                 :1;
        unsigned RBIE                   :1;
        unsigned INT0IE                 :1;
        unsigned TMR0IE                 :1;
        unsigned PEIE                   :1;
        unsigned GIE                    :1;
    };
    struct {
        unsigned RBIF                   :1;
        unsigned INT0IF                 :1;
        unsigned TMR0IF                 :1;
        unsigned RBIE                   :1;
        unsigned INT0IE                 :1;
        unsigned TMR0IE                 :1;
        unsigned GIEL                   :1;
        unsigned GIEH                   :1;
    };
    struct {
        unsigned RBIF                   :1;
        unsigned INT0IF                 :1;
        unsigned TMR0IF                 :1;
        unsigned RBIE                   :1;
        unsigned INT0IE                 :1;
        unsigned TMR0IE                 :1;
        unsigned PEIE_GIEL              :1;
        unsigned GIE_GIEH               :1;
    };
    struct {
        unsigned                        :1;
        unsigned INT0F                  :1;
        unsigned T0IF                   :1;
        unsigned                        :1;
        unsigned INT0E                  :1;
        unsigned T0IE                   :1;
        unsigned PEIE                   :1;
        unsigned GIE                    :1;
    };
    struct {
        unsigned                        :6;
        unsigned GIEL                   :1;
        unsigned GIEH                   :1;
    };
} INTCONbits @ 0xFF2;

// Register: PROD
extern volatile unsigned short          PROD                @ 0xFF3;
#ifndef _LIB_BUILD
asm("PROD equ 0FF3h");
#endif
// bitfield definitions
extern volatile union {
    struct {
        unsigned PROD                   :16;
    };
} PRODbits @ 0xFF3;

// Register: PRODL
extern volatile unsigned char           PRODL               @ 0xFF3;
#ifndef _LIB_BUILD
asm("PRODL equ 0FF3h");
#endif
// bitfield definitions
extern volatile union {
    struct {
        unsigned PRODL                  :8;
    };
} PRODLbits @ 0xFF3;

// Register: PRODH
extern volatile unsigned char           PRODH               @ 0xFF4;
#ifndef _LIB_BUILD
asm("PRODH equ 0FF4h");
#endif
// bitfield definitions
extern volatile union {
    struct {
        unsigned PRODH                  :8;
    };
} PRODHbits @ 0xFF4;

// Register: TABLAT
extern volatile unsigned char           TABLAT              @ 0xFF5;
#ifndef _LIB_BUILD
asm("TABLAT equ 0FF5h");
#endif
// bitfield definitions
extern volatile union {
    struct {
        unsigned TABLAT                 :8;
    };
} TABLATbits @ 0xFF5;

// Register: TBLPTR
extern volatile unsigned short long     TBLPTR              @ 0xFF6;
#ifndef _LIB_BUILD
asm("TBLPTR equ 0FF6h");
#endif
// bitfield definitions
extern volatile union {
    struct {
        unsigned TBLPTR                 :21;
        unsigned ACSS                   :1;
    };
} TBLPTRbits @ 0xFF6;

// Register: TBLPTRL
extern volatile unsigned char           TBLPTRL             @ 0xFF6;
#ifndef _LIB_BUILD
asm("TBLPTRL equ 0FF6h");
#endif
// bitfield definitions
extern volatile union {
    struct {
        unsigned TBLPTRL                :8;
    };
} TBLPTRLbits @ 0xFF6;

// Register: TBLPTRH
extern volatile unsigned char           TBLPTRH             @ 0xFF7;
#ifndef _LIB_BUILD
asm("TBLPTRH equ 0FF7h");
#endif
// bitfield definitions
extern volatile union {
    struct {
        unsigned TBLPTRH                :8;
    };
} TBLPTRHbits @ 0xFF7;

// Register: TBLPTRU
extern volatile unsigned char           TBLPTRU             @ 0xFF8;
#ifndef _LIB_BUILD
asm("TBLPTRU equ 0FF8h");
#endif
// bitfield definitions
extern volatile union {
    struct {
        unsigned TBLPTRU                :5;
        unsigned ACSS                   :1;
    };
} TBLPTRUbits @ 0xFF8;

// Register: PCLAT
extern volatile unsigned short long     PCLAT               @ 0xFF9;
#ifndef _LIB_BUILD
asm("PCLAT equ 0FF9h");
#endif
// aliases
extern volatile unsigned short long     PC                  @ 0xFF9;
#ifndef _LIB_BUILD
asm("PC equ 0FF9h");
#endif
// bitfield definitions
extern volatile union {
    struct {
        unsigned PCLAT                  :21;
    };
} PCLATbits @ 0xFF9;
// alias bitfield definitions
extern volatile union {
    struct {
        unsigned PCLAT                  :21;
    };
} PCbits @ 0xFF9;

// Register: PCL
extern volatile unsigned char           PCL                 @ 0xFF9;
#ifndef _LIB_BUILD
asm("PCL equ 0FF9h");
#endif
// bitfield definitions
extern volatile union {
    struct {
        unsigned PCL                    :8;
    };
} PCLbits @ 0xFF9;

// Register: PCLATH
extern volatile unsigned char           PCLATH              @ 0xFFA;
#ifndef _LIB_BUILD
asm("PCLATH equ 0FFAh");
#endif
// bitfield definitions
extern volatile union {
    struct {
        unsigned PCH                    :8;
    };
} PCLATHbits @ 0xFFA;

// Register: PCLATU
extern volatile unsigned char           PCLATU              @ 0xFFB;
#ifndef _LIB_BUILD
asm("PCLATU equ 0FFBh");
#endif
// bitfield definitions
extern volatile union {
    struct {
        unsigned PCU                    :5;
    };
} PCLATUbits @ 0xFFB;

// Register: STKPTR
extern volatile unsigned char           STKPTR              @ 0xFFC;
#ifndef _LIB_BUILD
asm("STKPTR equ 0FFCh");
#endif
// bitfield definitions
extern volatile union {
    struct {
        unsigned STKPTR                 :5;
        unsigned                        :1;
        unsigned STKUNF                 :1;
        unsigned STKFUL                 :1;
    };
    struct {
        unsigned SP0                    :1;
        unsigned SP1                    :1;
        unsigned SP2                    :1;
        unsigned SP3                    :1;
        unsigned SP4                    :1;
        unsigned                        :2;
        unsigned STKOVF                 :1;
    };
} STKPTRbits @ 0xFFC;

// Register: TOS
extern volatile unsigned short long     TOS                 @ 0xFFD;
#ifndef _LIB_BUILD
asm("TOS equ 0FFDh");
#endif
// bitfield definitions
extern volatile union {
    struct {
        unsigned TOS                    :21;
    };
} TOSbits @ 0xFFD;

// Register: TOSL
extern volatile unsigned char           TOSL                @ 0xFFD;
#ifndef _LIB_BUILD
asm("TOSL equ 0FFDh");
#endif
// bitfield definitions
extern volatile union {
    struct {
        unsigned TOSL                   :8;
    };
} TOSLbits @ 0xFFD;

// Register: TOSH
extern volatile unsigned char           TOSH                @ 0xFFE;
#ifndef _LIB_BUILD
asm("TOSH equ 0FFEh");
#endif
// bitfield definitions
extern volatile union {
    struct {
        unsigned TOSH                   :8;
    };
} TOSHbits @ 0xFFE;

// Register: TOSU
extern volatile unsigned char           TOSU                @ 0xFFF;
#ifndef _LIB_BUILD
asm("TOSU equ 0FFFh");
#endif
// bitfield definitions
extern volatile union {
    struct {
        unsigned TOSU                   :5;
    };
} TOSUbits @ 0xFFF;
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
